zsellera/openstint-transponder/docs/antenna-tuning.asc

C1: cap; 3.7n
C2: cap; 2n
C3: cap; 1.3n
C4: cap; 910p
C5: cap; 490p
C6: cap; 450p
C7: cap; 1n
C8: cap; 1n
C9: cap; 680p
C10: cap; 866p
C11: cap; 910p
C12: cap; 680p
C13: cap; 1.2n
C14: cap; 2n
C15: cap; 750p
C16: cap; 560p
L1: ind2; 1.72µ
L2: ind2; 0.72µ
L3: ind2; 3.3µ
L4: ind; 350n
L5: ind2; 0.72µ
L6: ind2; 0.72µ
L7: ind; 350n
L8: ind2; 0.848µ
R1: res; 33
R2: res; 60
R3: res; 60
R4: res; 11
R5: res; 33
R6: res; 25
R7: res; 11
R8: res; 25
V1: voltage; PULSE(0 6 1u 10n 10n 90n 200n 8); AC 1
Named nets: 0
;.ac dec 1000 1meg 10meg
.tran 5u
4x2 turn
4x3t
4x4t
v1 onboard
4x2 mas topologia
v1 +40%
Imax=120mA\\
4x2 mas topologia, Q=3
v1 +40%
Imax = 150mA
v1 re-tune
v1 +80%
Imax=350mA
4x2 mas topologia, nagyobb board, Q=4
v1 +40%
Imax = 150mA
