zsellera/openstint-transponder/docs/coupled-antenna-v1.asc

C1: cap; 2n
C2: cap; 1n
L1: ind2; 0.2µ
L2: ind2; 0.5µ
M1: nmos; 2N7002
R1: res; 1
R2: res; 22
R3: res; 1
R4: res; 1k
R5: res; 2
R6: res; 10
V1: voltage; 3.3
V2: voltage; PULSE(0 3.3 1000n 4n 4n 96n 200n 8)
Named nets: 0
K L1 L2 0.95
.tran 5u
