zsellera/openstint-transponder/docs/antenna2.asc

C1: cap; 680p
C2: cap; 750p
C3: cap; 1.3n
C4: cap; 910p
C5: cap; 2.5n
C6: cap; 1.1n
C7: cap; 470p
C8: cap; 680p
L1: ind; 2.6µ
L2: ind; 1.84µ
L3: ind; 1.3µ
L4: ind; 2.6µ
R1: res; 68
R2: res; 68
R3: res; 68
R4: res; 22
V1: voltage; PULSE(0 6.6 0 1n 1n 99n 200n); AC 1
V2: voltage; PULSE(0 6.6 0 1n 1n 99n 200n); AC 1
Named nets: 0
;.ac dec 1000 1meg 100meg
.tran 1n 5u
High current solution with push-pull driver
Low current solution with MCU pins
